zhbi98/MotorFOC/HardWare/kiacd_project/MotorKit.kicad_sch

## KiCad design HardWare/kiacd_project/MotorKit.kicad_sch (2024-01-31)

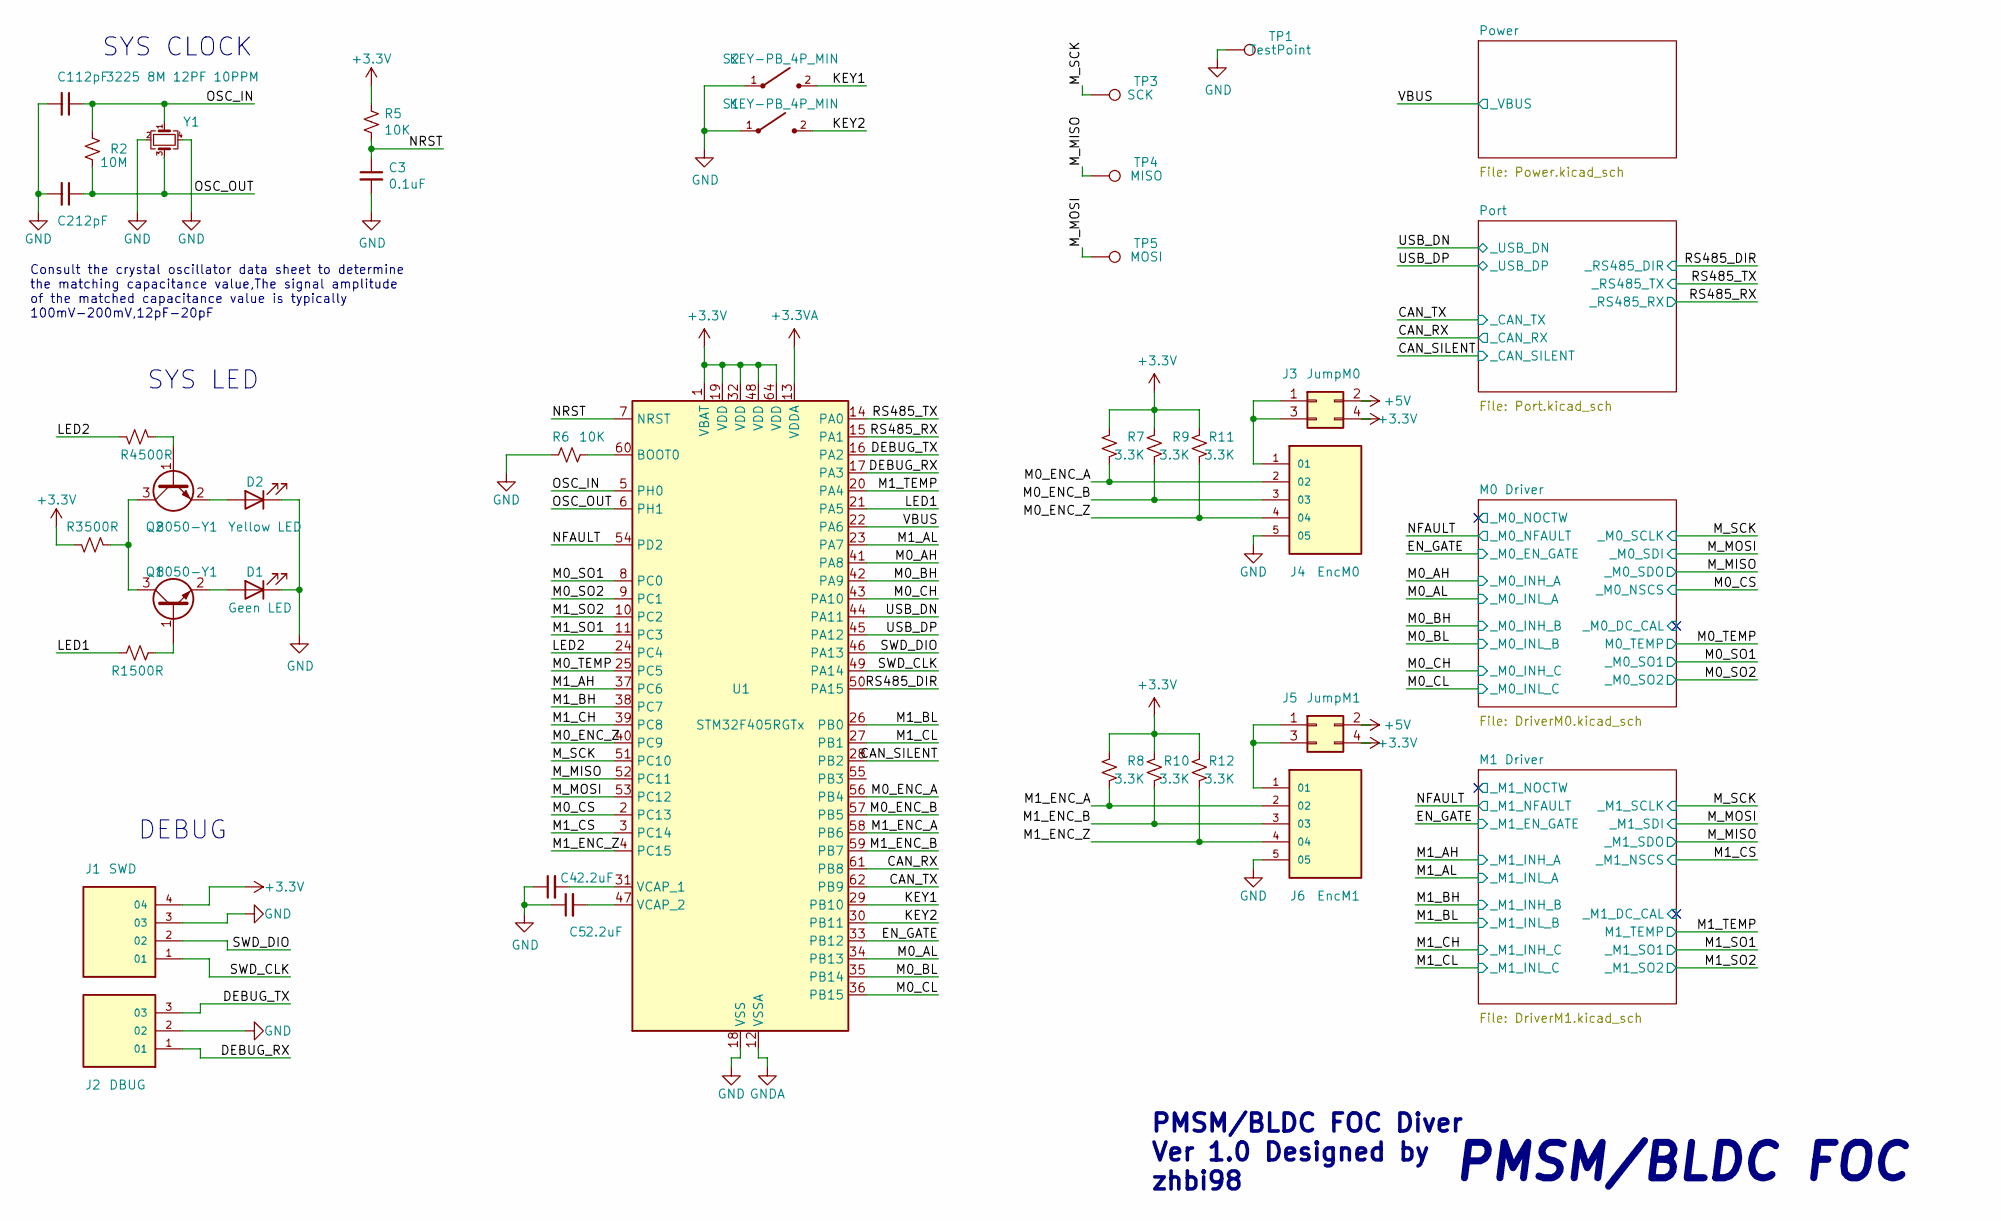
[picture p7: schematic MotorKit.kicad_sch]

Parts:
C1, C2: 12pF; C_0603_1608Metric
C3: 0.1uF; C_0603_1608Metric
C4, C5: 2.2uF; C_0603_1608Metric
D1: Geen LED; LED_0603_1608Metric
D2: Yellow LED; LED_0603_1608Metric
J1: SWD; CONN-SMD_1x4P-P1.0-H_WAFER-SH1.0-4PWB
J2: DBUG; CONN-SMD_1x3P-P1.0-H_WAFER-SH1.0-3PWB
J3: JumpM0; PinHeader_2x02_P1.27mm_Vertical_SMD
J4: EncM0; CONN-SMD_1x5P-P1.0-H_WAFER-SH1.0-5PWB
J5: JumpM1; PinHeader_2x02_P1.27mm_Vertical_SMD
J6: EncM1; CONN-SMD_1x5P-P1.0-H_WAFER-SH1.0-5PWB
Q1, Q2: 8050-Y1; SOT-23
R1, R3, R4: 500R; R_0603_1608Metric
R2: 10M; R_0603_1608Metric
R5, R6: 10K; R_0603_1608Metric
R7, R8, R9, R10, R11, R12: 3.3K; R_0603_1608Metric
S1, S2: KEY-PB_4P_MIN; KEY-SMD_2P_L4.0-W3.0-V_K2-1807SN-A3DW-06
TP1: TestPoint; TestPoint_Pad_D1.0mm
TP3: SCK; TestPoint_Pad_D1.0mm
TP4: MISO; TestPoint_Pad_D1.0mm
TP5: MOSI; TestPoint_Pad_D1.0mm
U1: STM32F405RGTx; LQFP-64_10x10mm_P0.5mm
Y1: 3225 8M 12PF 10PPM; Crystal_SMD_3225-4Pin_3.2x2.5mm

Connections:
+3.3V: J1.4, J3.4, J5.4, R3.2, R5.1, R7.1, R8.1, R9.1, R10.1, R11.1, R12.1, U1.1 (VBAT), U1.19 (VDD), U1.32 (VDD), U1.48 (VDD), U1.64 (VDD)
+3.3VA: U1.13 (VDDA)
+5V: J3.2, J5.2
CAN_RX: U1.61 (PB8)
CAN_SILENT: U1.28 (PB2)
CAN_TX: U1.62 (PB9)
DEBUG_RX: J2.1, U1.17 (PA3)
DEBUG_TX: J2.3, U1.16 (PA2)
EN_GATE: U1.33 (PB12)
GND: C1.2, C2.2, C3.2, C4.1, C5.1, D1.1 (K), D2.1 (K), J1.3, J2.2, J4.5, J6.5, R6.2, S1.1, S2.1, TP1.1, U1.18 (VSS), U1.63 (VSS), Y1.2, Y1.4
GNDA: U1.12 (VSSA)
KEY1: S2.2, U1.29 (PB10)
KEY2: S1.2, U1.30 (PB11)
LED1: R1.2, U1.21 (PA5)
LED2: R4.2, U1.24 (PC4)
M0_AH: U1.41 (PA8)
M0_AL: U1.34 (PB13)
M0_BH: U1.42 (PA9)
M0_BL: U1.35 (PB14)
M0_CH: U1.43 (PA10)
M0_CL: U1.36 (PB15)
M0_CS: U1.2 (PC13)
M0_ENC_A: J4.2, R7.2, U1.56 (PB4)
M0_ENC_B: J4.3, R9.2, U1.57 (PB5)
M0_ENC_Z: J4.4, R11.2, U1.40 (PC9)
M0_SO1: U1.8 (PC0)
M0_SO2: U1.9 (PC1)
M0_TEMP: U1.25 (PC5)
M1_AH: U1.37 (PC6)
M1_AL: U1.23 (PA7)
M1_BH: U1.38 (PC7)
M1_BL: U1.26 (PB0)
M1_CH: U1.39 (PC8)
M1_CL: U1.27 (PB1)
M1_CS: U1.3 (PC14)
M1_ENC_A: J6.2, R8.2, U1.58 (PB6)
M1_ENC_B: J6.3, R10.2, U1.59 (PB7)
M1_ENC_Z: J6.4, R12.2, U1.4 (PC15)
M1_SO1: U1.11 (PC3)
M1_SO2: U1.10 (PC2)
M1_TEMP: U1.20 (PA4)
M_MISO: TP4.1, U1.52 (PC11)
M_MOSI: TP5.1, U1.53 (PC12)
M_SCK: TP3.1, U1.51 (PC10)
NFAULT: U1.54 (PD2)
NRST: C3.1, R5.2, U1.7 (NRST)
unnamed: C4.2, U1.31 (VCAP_1)
unnamed: C5.2, U1.47 (VCAP_2)
unnamed: D1.2 (A), Q1.2 (E)
unnamed: D2.2 (A), Q2.2 (E)
unnamed: J3.1, J3.3, J4.1
unnamed: J5.1, J5.3, J6.1
unnamed: Q1.1 (B), R1.1
unnamed: Q1.3 (C), Q2.3 (C), R3.1
unnamed: Q2.1 (B), R4.1
unnamed: R6.1, U1.60 (BOOT0)
OSC_IN: C1.1, R2.2, U1.5 (PH0), Y1.1
OSC_OUT: C2.1, R2.1, U1.6 (PH1), Y1.3
RS485_DIR: U1.50 (PA15)
RS485_RX: U1.15 (PA1)
RS485_TX: U1.14 (PA0)
SWD_CLK: J1.1, U1.49 (PA14)
SWD_DIO: J1.2, U1.46 (PA13)
USB_DN: U1.44 (PA11)
USB_DP: U1.45 (PA12)
VBUS: U1.22 (PA6)

Notes on the sheet:
DEBUG
SYS LED
PMSM/BLDC FOC Diver Ver 1.0 Designed by zhbi98
Consult the crystal oscillator data sheet to determine the matching capacitance value,The signal amplitude of the matched capacitance value is typically 100mV-200mV,12pF-20pF
SYS CLOCK
PMSM/BLDC FOC
