zhbi98/MotorFOC/Firmware/main/main.h

/**
 * @file main.h
 *
 */

#ifndef __MAIN_H__
#define __MAIN_H__

/*********************
 *      INCLUDES
 *********************/

#include "stm32f4xx_hal.h"

/**********************
 * GLOBAL PROTOTYPES
 **********************/

void Error_Handler(void);

#endif /*__MAIN_H__*/
